LaskaKit/ESP-Vindriktning/img/03.jpg

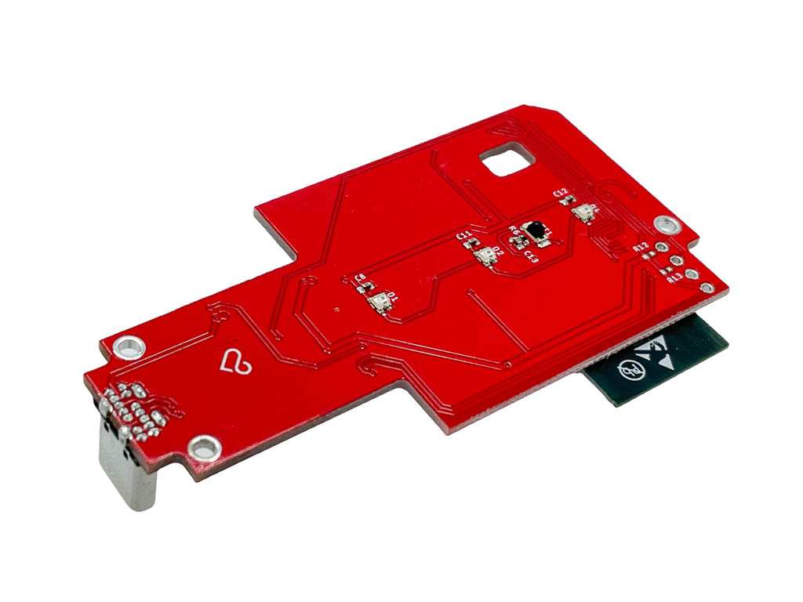
img/03.jpg
